benadski/badge/src/tv-b-fri3d/WORLDcodes.cpp

/*
TV-B-Gone for Arduino version 0.001
Ported to Arduino by Ken Shirriff, Dec 3, 2009
http://arcfn.com

The original code is:
TV-B-Gone Firmware version 1.2
 for use with ATtiny85v and v1.2 hardware
 (c) Mitch Altman + Limor Fried 2009
 
2-September-2015
Updated definitions for 
     const struct IrCode *EUpowerCodes[] PROGMEM = {
and
     const struct IrCode *NApowerCodes[] PROGMEM = {
so that the sketch will compile with Arduino 1.6.5 software.
The new definitions are:
     extern "C" const struct IrCode * const EUpowerCodes[] PROGMEM = {
and
     extern "C" const struct IrCode * const NApowerCodes[] PROGMEM = {
so that the sketch will compile with Arduino 1.6.5 software.

*/


#include "main.h"

//Codes captured from Generation 3 TV-B-Gone by Limor Fried & Mitch Altman
// table of POWER codes

const uint16_t code_na000Times[] PROGMEM = {
  60, 60,
  60, 2700,
  120, 60,
  240, 60,
};
const uint8_t code_na000Codes[] PROGMEM = {
  0xE2,
  0x20,
  0x80,
  0x78,
  0x88,
  0x20,
  0x10,
};
const struct IrCode code_na000Code PROGMEM = {
  freq_to_timerval(38400),
  26,             // # of pairs
  2,              // # of bits per index
  code_na000Times,
  code_na000Codes
};

const uint16_t code_na001Times[] PROGMEM = {
  50, 100,
  50, 200,
  50, 800,
  400, 400,
};
const uint8_t code_na001Codes[] PROGMEM = {
  0xD5,
  0x41,
  0x11,
  0x00,
  0x14,
  0x44,
  0x6D,
  0x54,
  0x11,
  0x10,
  0x01,
  0x44,
  0x45,
};
const struct IrCode code_na001Code PROGMEM = {
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
 	50, 50,
 	50, 99,
 	50, 251,
 	50, 252,
 	50, 1449,
 	50, 11014,
 	102, 49,
 	102, 98,
 };
 */
const uint8_t code_eu130Codes[] PROGMEM = {
  0x47,
  0x00,
  0x00,
  0x00,
  0x00,
  0x00,
  0x8C,
  0x8C,
  0x40,
  0x03,
  0xE3,
  0xEB,
  0x23,
  0x10,
  0x00,
  0xF8,
  0xF4,
};
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
